rsandrini/D20-IRL-detection/3d_model/imgs/2.jpg

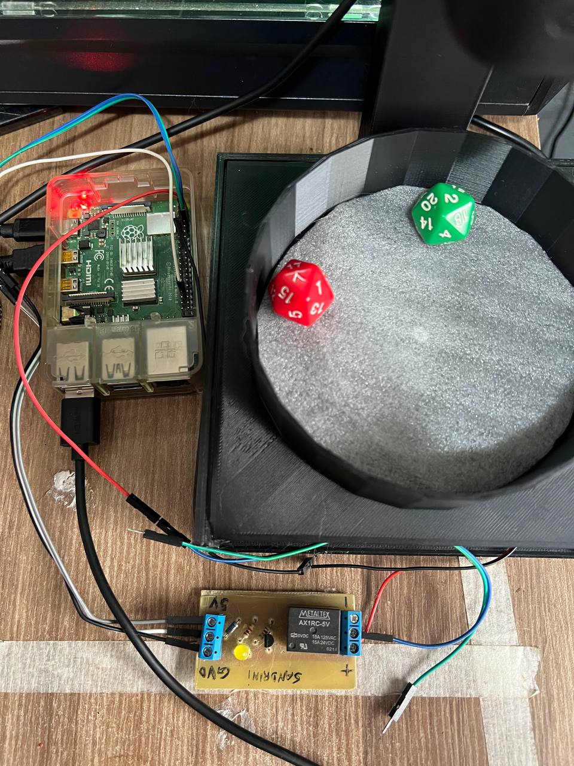
3d_model/imgs/2.jpg
