rsandrini/D20-IRL-detection/3d_model/imgs/3.jpg

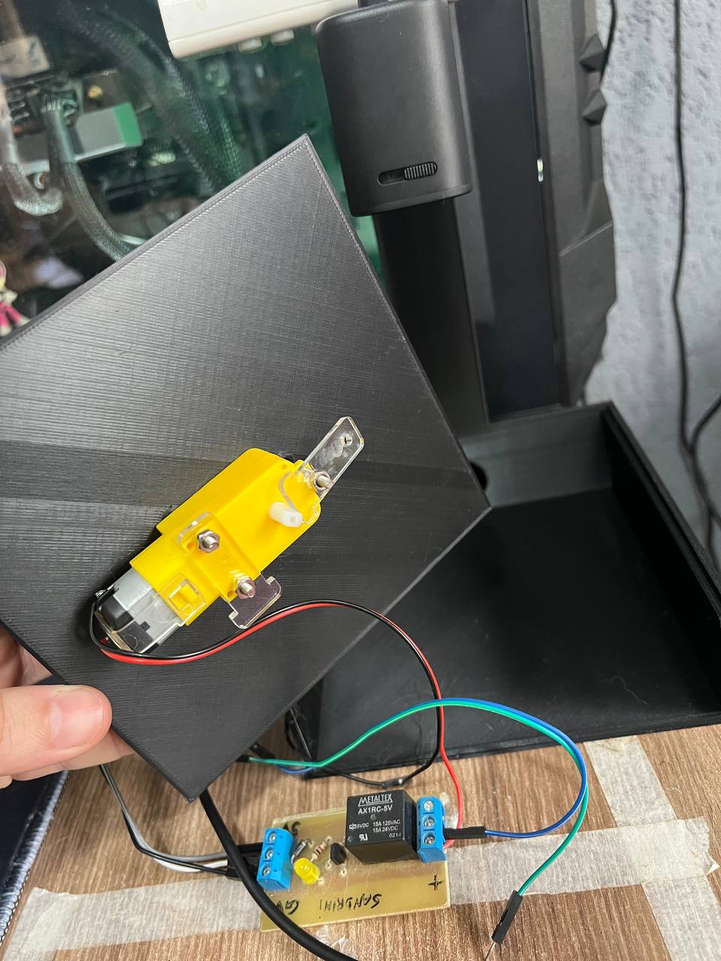
3d_model/imgs/3.jpg
