rsandrini/D20-IRL-detection/3d_model/imgs/4.jpg

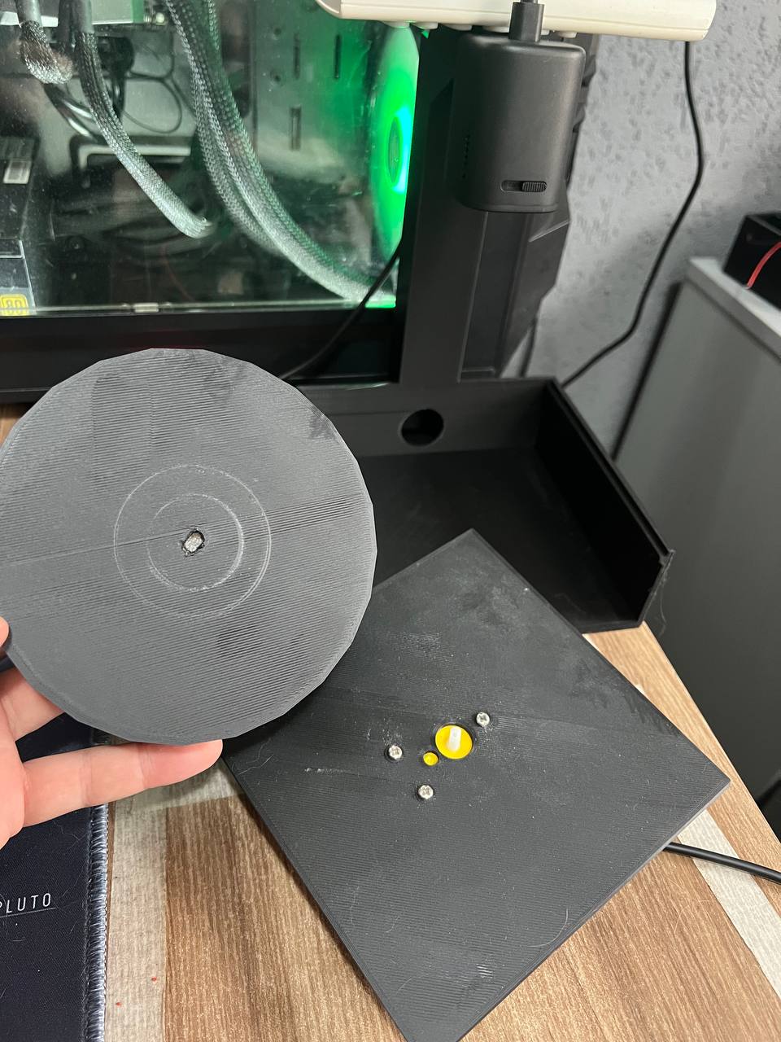
3d_model/imgs/4.jpg
