rsandrini/D20-IRL-detection/3d_model/imgs/5.jpg

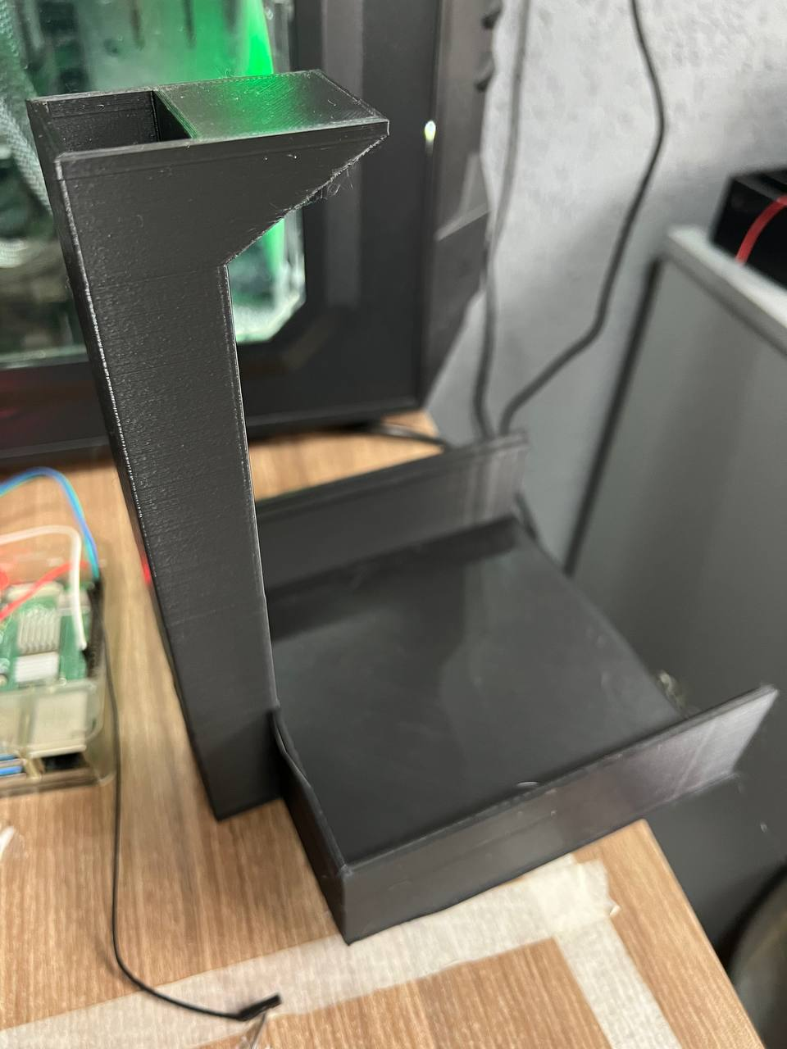
3d_model/imgs/5.jpg
