rsandrini/D20-IRL-detection/data/images/val/roll_0003_9260f4.jpg

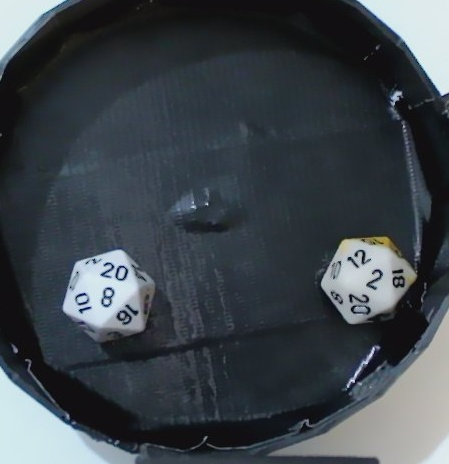
data/images/val/roll_0003_9260f4.jpg
