rsandrini/D20-IRL-detection/data/images/val/roll_0004_5c2b91.jpg

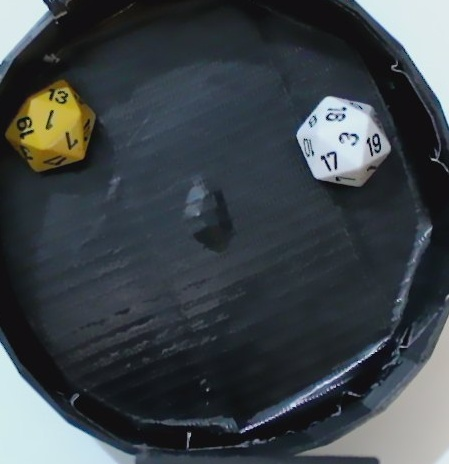
data/images/val/roll_0004_5c2b91.jpg
