rsandrini/D20-IRL-detection/data/images/val/roll_0006_699569.jpg

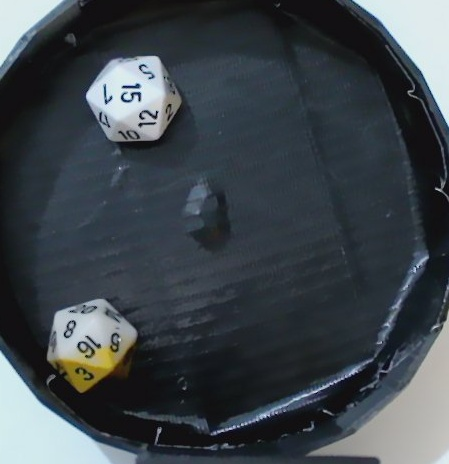
data/images/val/roll_0006_699569.jpg
