rsandrini/D20-IRL-detection/data/images/val/roll_0013_bd96cc.jpg

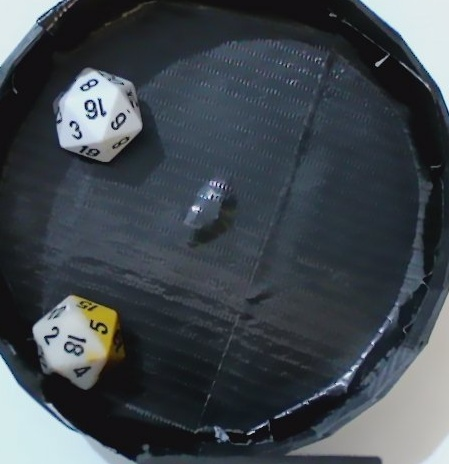
data/images/val/roll_0013_bd96cc.jpg
