rsandrini/D20-IRL-detection/data/images/val/roll_0014_3a582c.jpg

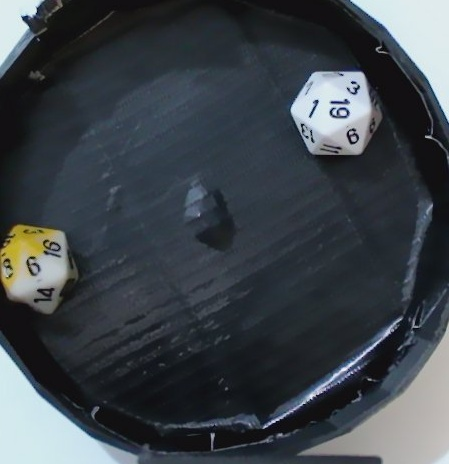
data/images/val/roll_0014_3a582c.jpg
