rsandrini/D20-IRL-detection/data/images/val/roll_0016_4558c0.jpg

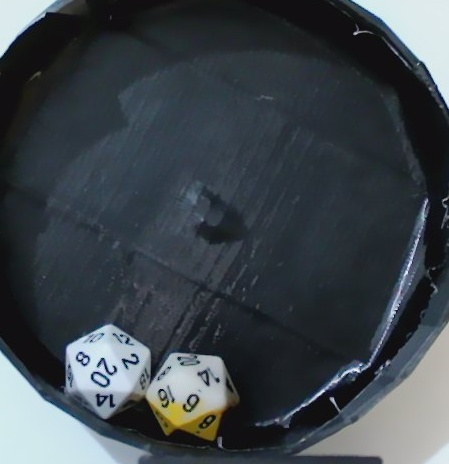
data/images/val/roll_0016_4558c0.jpg
