rsandrini/D20-IRL-detection/data/images/val/roll_0031_e9eac3.jpg

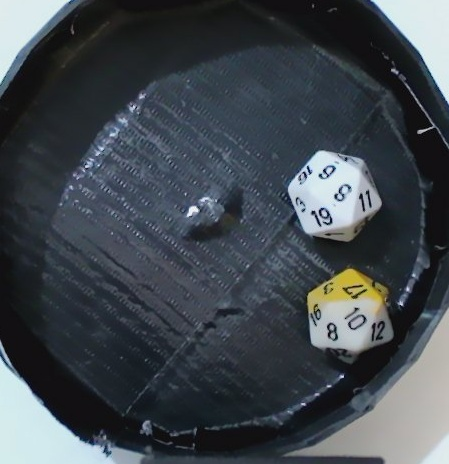
data/images/val/roll_0031_e9eac3.jpg
