rsandrini/D20-IRL-detection/data/images/val/roll_0033_6a69eb.jpg

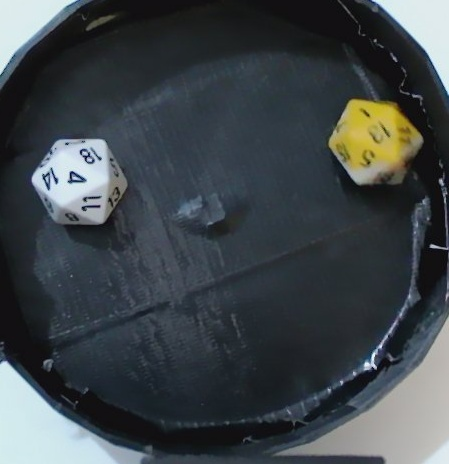
data/images/val/roll_0033_6a69eb.jpg
