rsandrini/D20-IRL-detection/data/images/val/roll_0037_a4c2fc.jpg

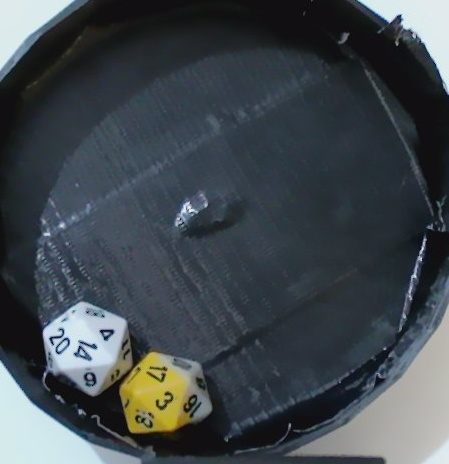
data/images/val/roll_0037_a4c2fc.jpg
