rsandrini/D20-IRL-detection/data/images/val/roll_0038_ef2dc1.jpg

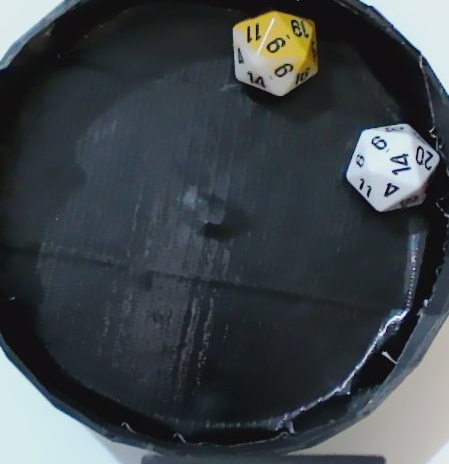
data/images/val/roll_0038_ef2dc1.jpg
