rsandrini/D20-IRL-detection/data/images/val/roll_0043_4cf03e.jpg

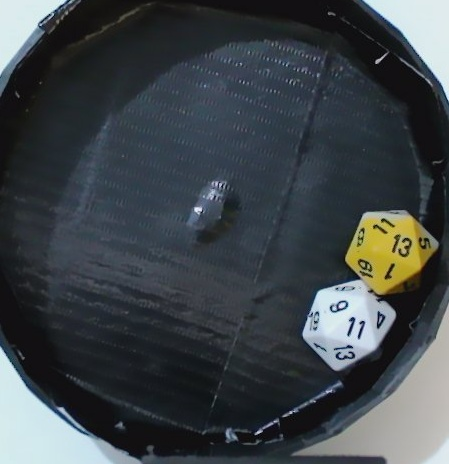
data/images/val/roll_0043_4cf03e.jpg
