rsandrini/D20-IRL-detection/data/images/val/roll_0045_0b2040.jpg

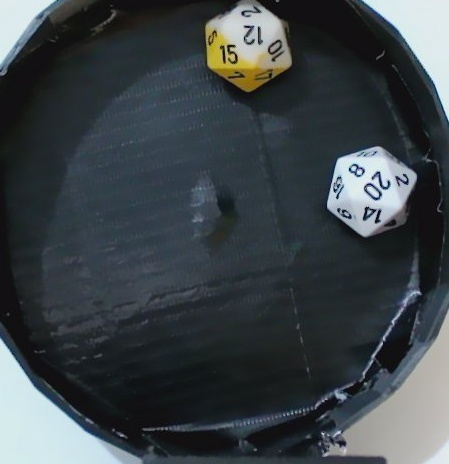
data/images/val/roll_0045_0b2040.jpg
