rsandrini/D20-IRL-detection/data/images/val/roll_0046_d0351c.jpg

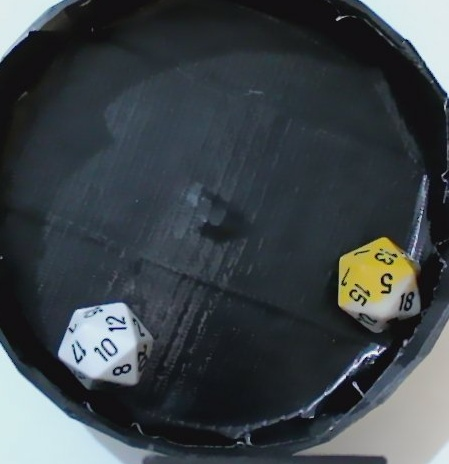
data/images/val/roll_0046_d0351c.jpg
