rsandrini/D20-IRL-detection/data/images/val/roll_0048_6ab94f.jpg

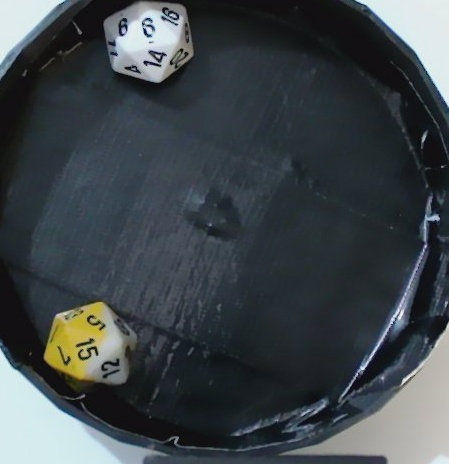
data/images/val/roll_0048_6ab94f.jpg
