rsandrini/D20-IRL-detection/data/images/val/roll_0062_7c9000.jpg

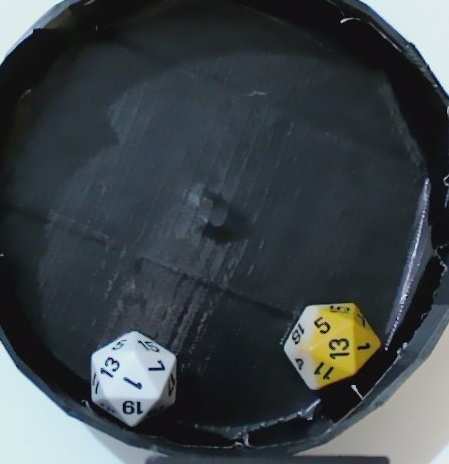
data/images/val/roll_0062_7c9000.jpg
