rsandrini/D20-IRL-detection/data/images/val/roll_0065_9c6021.jpg

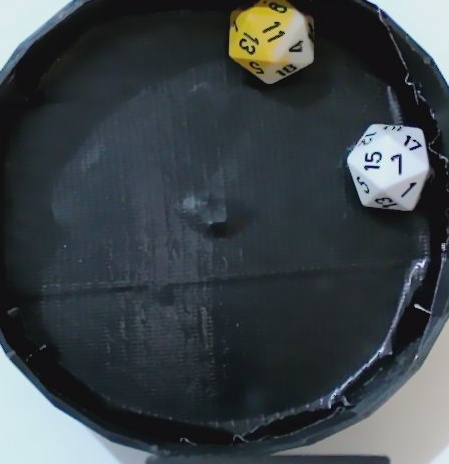
data/images/val/roll_0065_9c6021.jpg
