rsandrini/D20-IRL-detection/data/images/val/roll_0067_908758.jpg

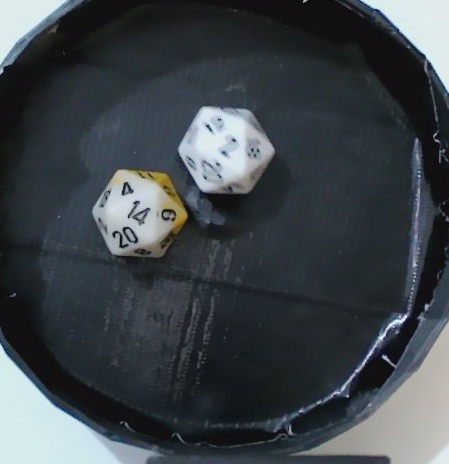
data/images/val/roll_0067_908758.jpg
