rsandrini/D20-IRL-detection/data/images/val/roll_0070_61421d.jpg

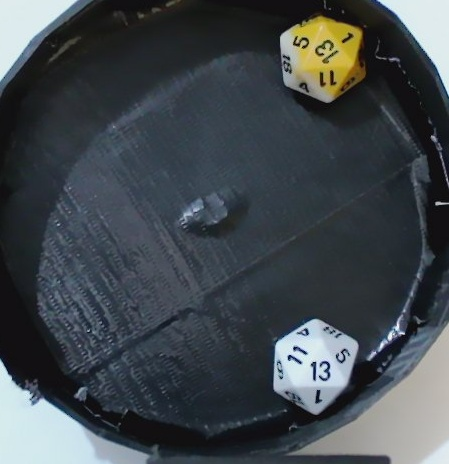
data/images/val/roll_0070_61421d.jpg
