rsandrini/D20-IRL-detection/data/images/val/roll_0077_c047f7.jpg

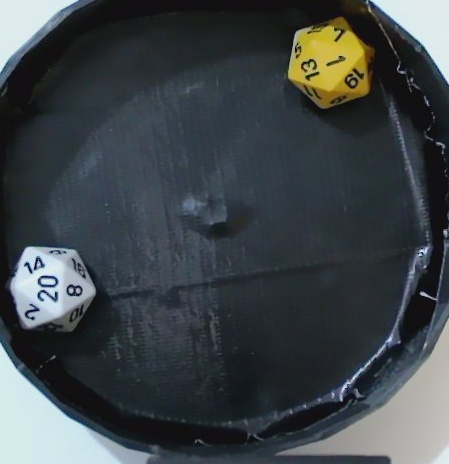
data/images/val/roll_0077_c047f7.jpg
