rsandrini/D20-IRL-detection/data/images/val/roll_0102_18575e.jpg

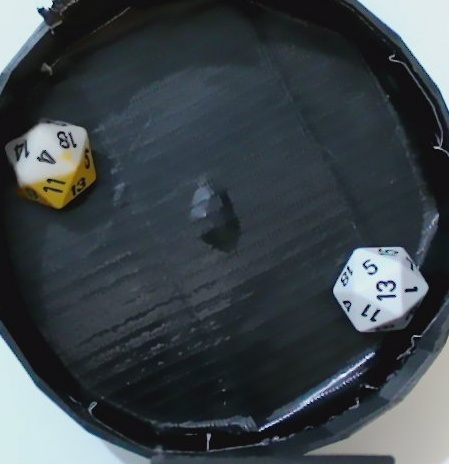
data/images/val/roll_0102_18575e.jpg
