rsandrini/D20-IRL-detection/data/images/val/roll_0111_e147ee.jpg

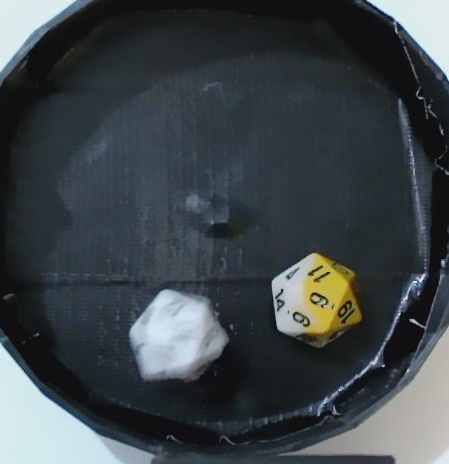
data/images/val/roll_0111_e147ee.jpg
