rsandrini/D20-IRL-detection/data/images/val/roll_0112_fa6df9.jpg

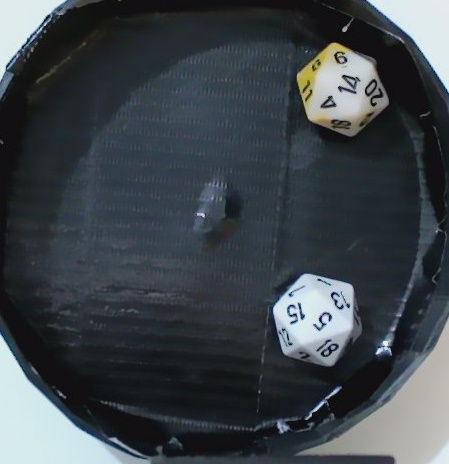
data/images/val/roll_0112_fa6df9.jpg
