rsandrini/D20-IRL-detection/data/images/val/roll_0122_8daa32.jpg

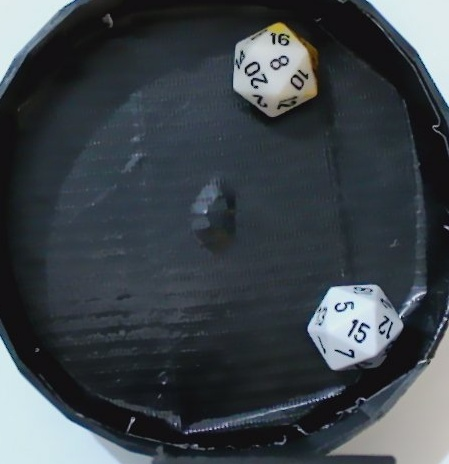
data/images/val/roll_0122_8daa32.jpg
