rsandrini/D20-IRL-detection/data/images/val/roll_0123_5c0753.jpg

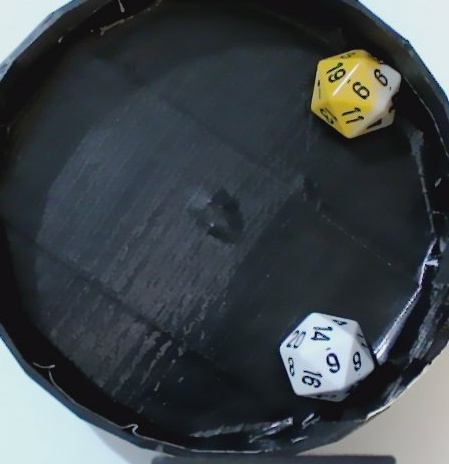
data/images/val/roll_0123_5c0753.jpg
