rsandrini/D20-IRL-detection/data/images/val/roll_0127_2e7928.jpg

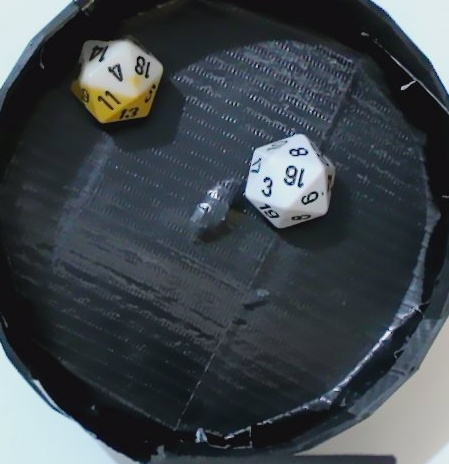
data/images/val/roll_0127_2e7928.jpg
