rsandrini/D20-IRL-detection/data/images/val/roll_0129_56e177.jpg

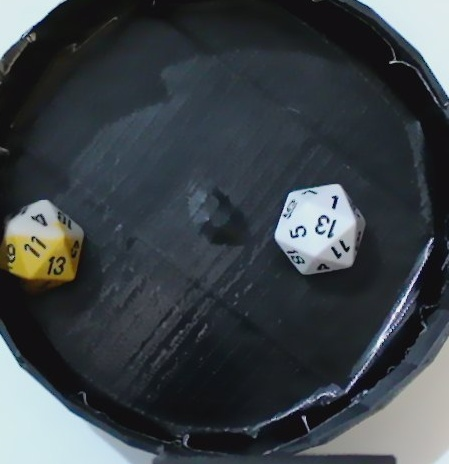
data/images/val/roll_0129_56e177.jpg
