rsandrini/D20-IRL-detection/data/images/val/roll_0131_5401d8.jpg

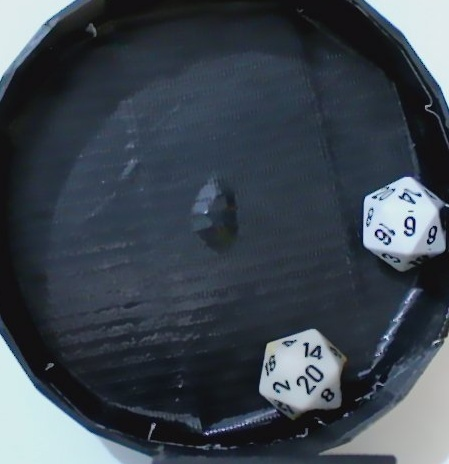
data/images/val/roll_0131_5401d8.jpg
