rsandrini/D20-IRL-detection/data/images/val/roll_0137_ff023d.jpg

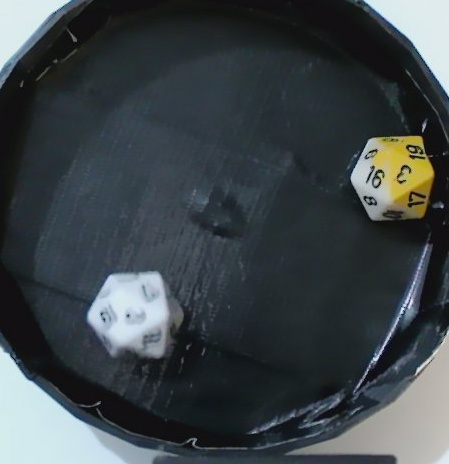
data/images/val/roll_0137_ff023d.jpg
