rsandrini/D20-IRL-detection/data/images/val/roll_0154_236faf.jpg

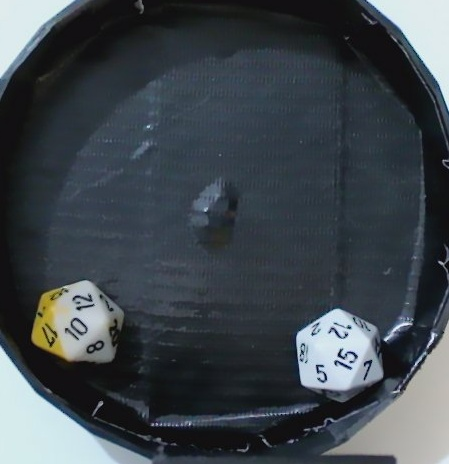
data/images/val/roll_0154_236faf.jpg
