rsandrini/D20-IRL-detection/data/images/val/roll_0159_bd059c.jpg

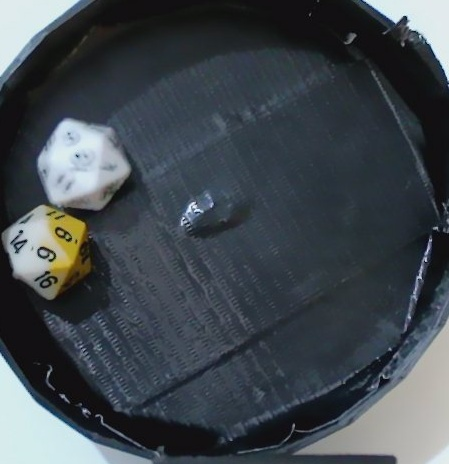
data/images/val/roll_0159_bd059c.jpg
