rsandrini/D20-IRL-detection/data/images/val/roll_0160_444020.jpg

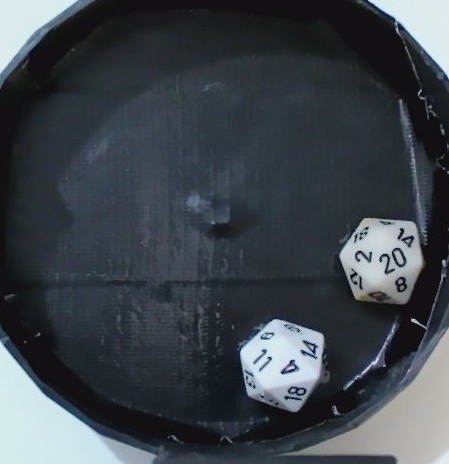
data/images/val/roll_0160_444020.jpg
