rsandrini/D20-IRL-detection/data/images/val/roll_0163_bad7c1.jpg

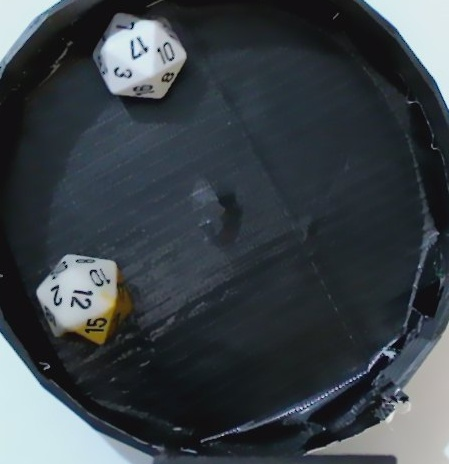
data/images/val/roll_0163_bad7c1.jpg
