rsandrini/D20-IRL-detection/data/images/val/roll_0168_1e1c85.jpg

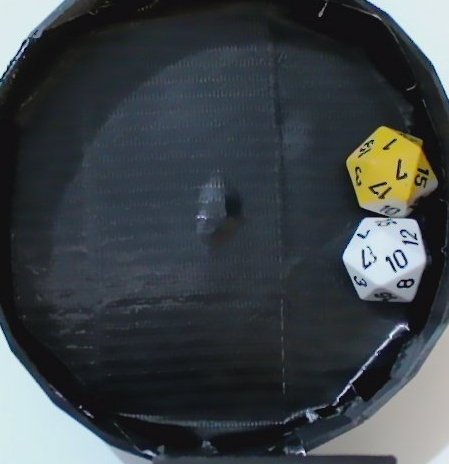
data/images/val/roll_0168_1e1c85.jpg
