rsandrini/D20-IRL-detection/data/images/val/roll_0171_e6abc9.jpg

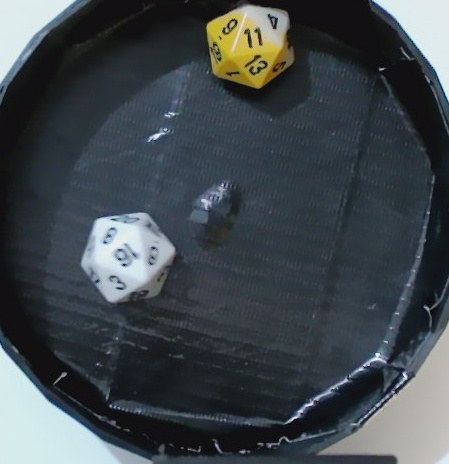
data/images/val/roll_0171_e6abc9.jpg
