rsandrini/D20-IRL-detection/data/images/val/roll_0173_381584.jpg

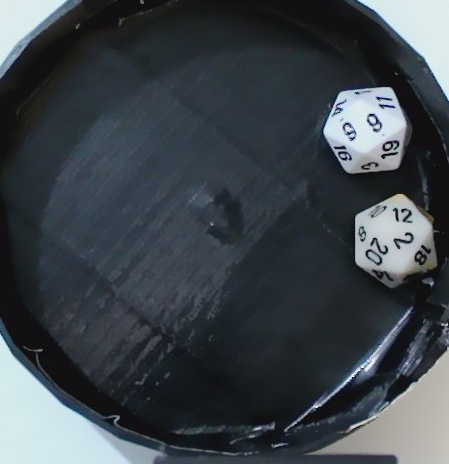
data/images/val/roll_0173_381584.jpg
