rsandrini/D20-IRL-detection/data/images/val/roll_0187_8b234c.jpg

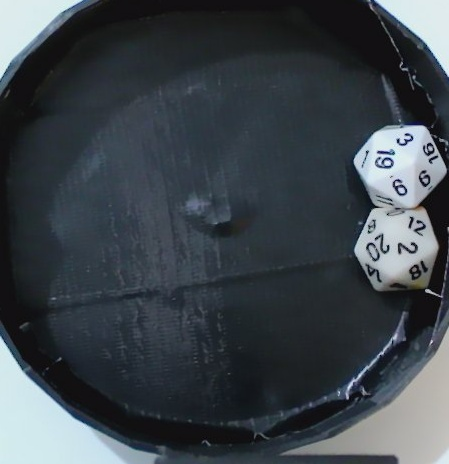
data/images/val/roll_0187_8b234c.jpg
