rsandrini/D20-IRL-detection/data/images/val/roll_0188_95a398.jpg

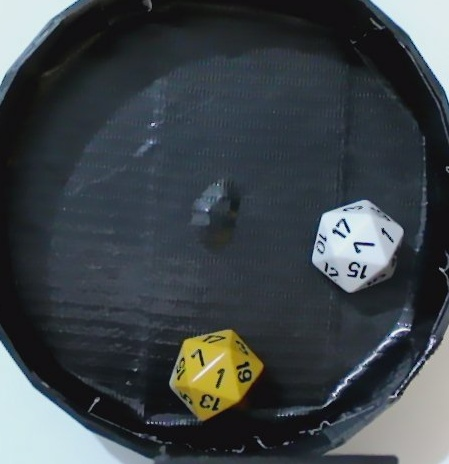
data/images/val/roll_0188_95a398.jpg
