rsandrini/D20-IRL-detection/data/images/val/roll_0194_2706d9.jpg

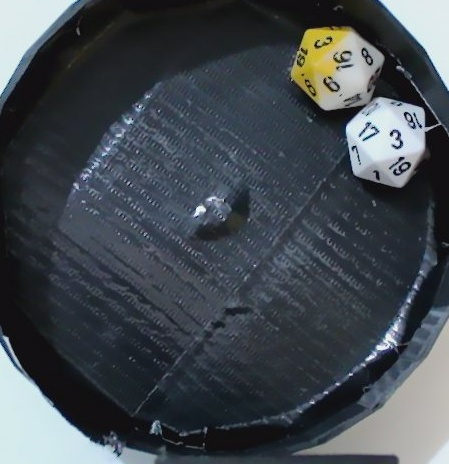
data/images/val/roll_0194_2706d9.jpg
