rsandrini/D20-IRL-detection/data/images/val/roll_0195_a73f36.jpg

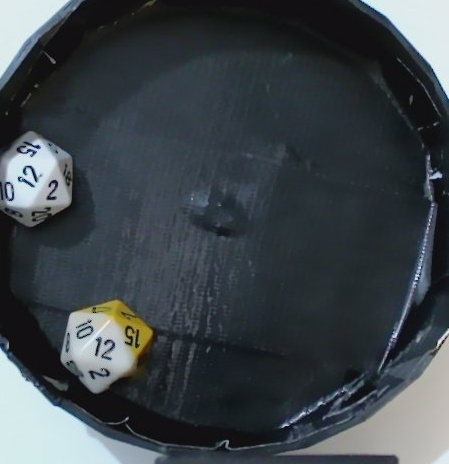
data/images/val/roll_0195_a73f36.jpg
