rsandrini/D20-IRL-detection/data/images/val/roll_0196_e32400.jpg

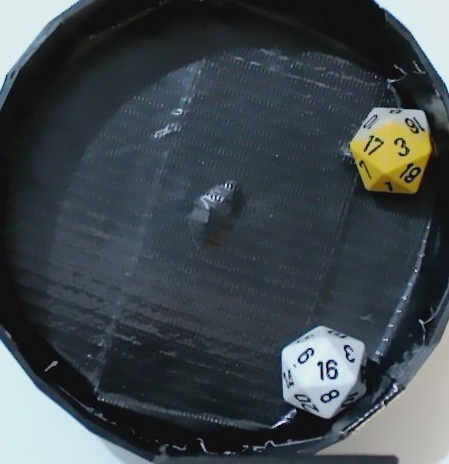
data/images/val/roll_0196_e32400.jpg
