rsandrini/D20-IRL-detection/static/results/0ec7581d-a79f-41ec-bebb-41047d4bcfe1.jpg

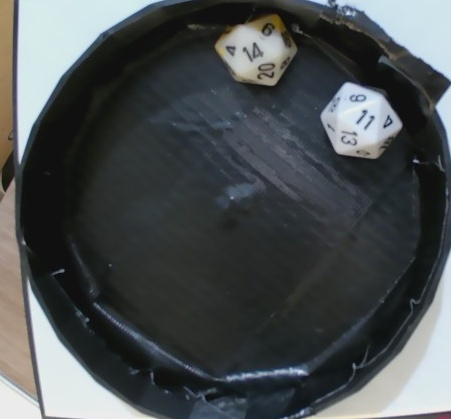
static/results/0ec7581d-a79f-41ec-bebb-41047d4bcfe1.jpg
