rsandrini/D20-IRL-detection/static/results/1f2905ae-a408-4a8b-bb5f-29edec2092f3.jpg

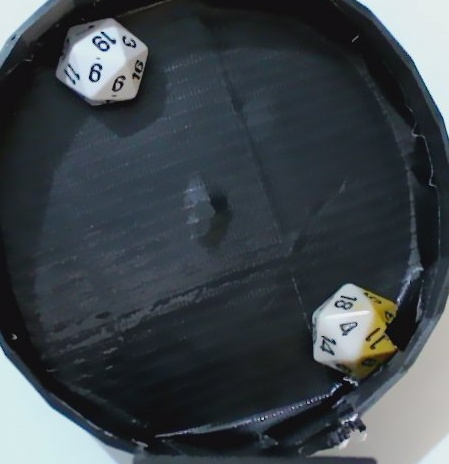
static/results/1f2905ae-a408-4a8b-bb5f-29edec2092f3.jpg
