rsandrini/D20-IRL-detection/static/results/2d5dee4a-9d91-4876-b8cb-90a706628ac4.jpg

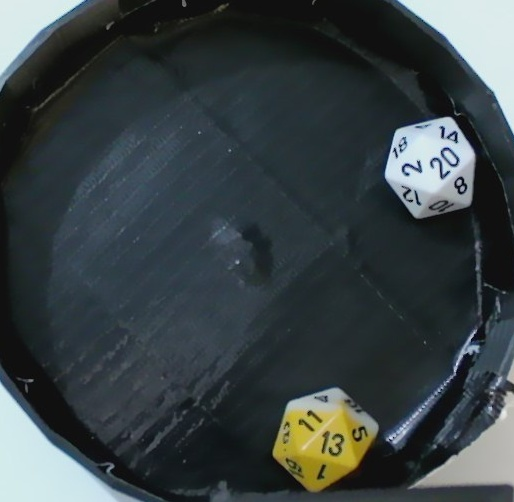
static/results/2d5dee4a-9d91-4876-b8cb-90a706628ac4.jpg
