rsandrini/D20-IRL-detection/static/results/63ee4cc3-fca6-4ec0-a35e-1c4646e539cd.gif

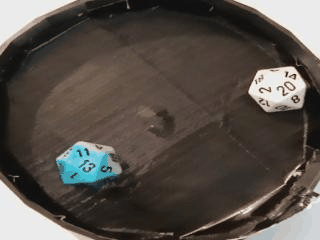
static/results/63ee4cc3-fca6-4ec0-a35e-1c4646e539cd.gif
