rsandrini/D20-IRL-detection/static/results/75d9a677-4451-443c-803d-1ba4c33d57f9.jpg

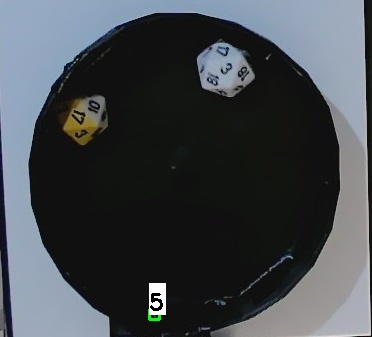
static/results/75d9a677-4451-443c-803d-1ba4c33d57f9.jpg
