rsandrini/D20-IRL-detection/static/results/223f2116-806a-4e07-b7c2-eb1def2b251b.jpg

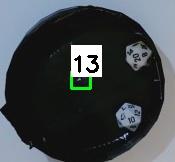
static/results/223f2116-806a-4e07-b7c2-eb1def2b251b.jpg
