rsandrini/D20-IRL-detection/static/results/428e884d-69d0-4718-a8a9-e1feac12c718.jpg

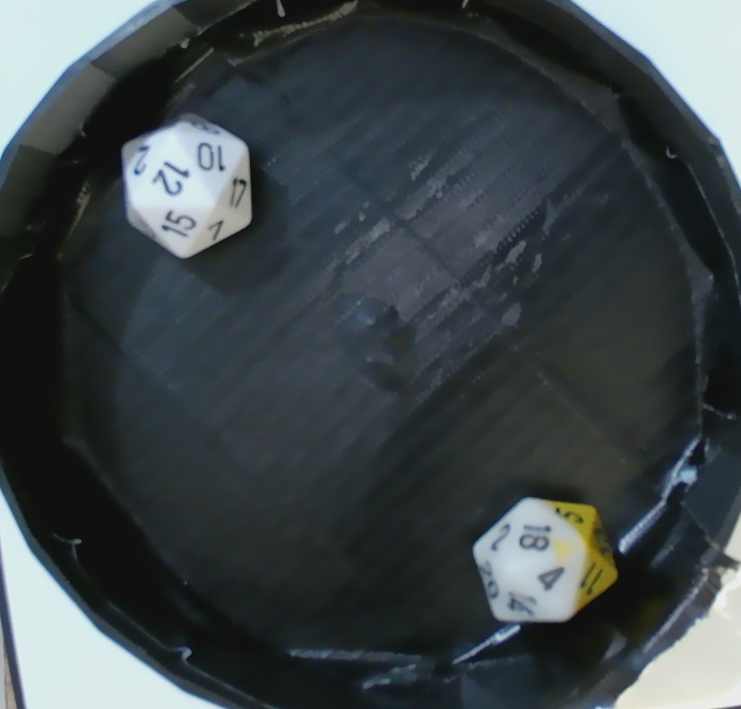
static/results/428e884d-69d0-4718-a8a9-e1feac12c718.jpg
