rsandrini/D20-IRL-detection/static/results/505b5c6e-b854-461b-a9c2-39d6cff4a146.jpg

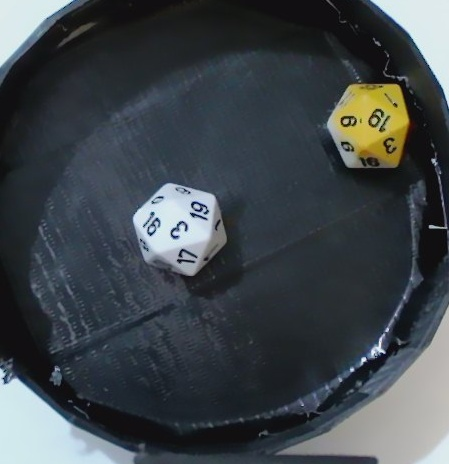
static/results/505b5c6e-b854-461b-a9c2-39d6cff4a146.jpg
