rsandrini/D20-IRL-detection/static/results/600d41de-3759-4a8f-982c-8f376b47929a.jpg

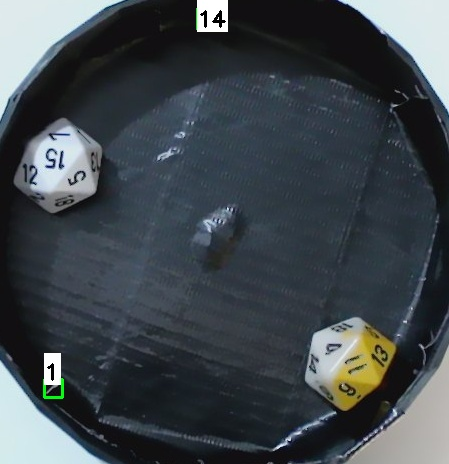
static/results/600d41de-3759-4a8f-982c-8f376b47929a.jpg
