rsandrini/D20-IRL-detection/static/results/2539a522-f37b-4129-82e0-7a8c40de38be.jpg

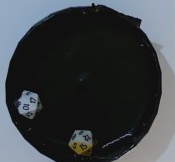
static/results/2539a522-f37b-4129-82e0-7a8c40de38be.jpg
