rsandrini/D20-IRL-detection/static/results/2985c857-9b9b-49bc-b022-46b17c431721.gif

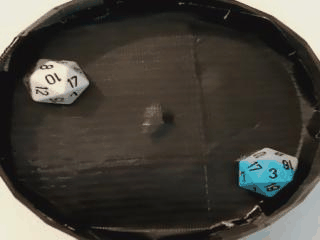
static/results/2985c857-9b9b-49bc-b022-46b17c431721.gif
