rsandrini/D20-IRL-detection/static/results/4426a67b-6e3e-4b60-9d31-17f29a3e8788.jpg

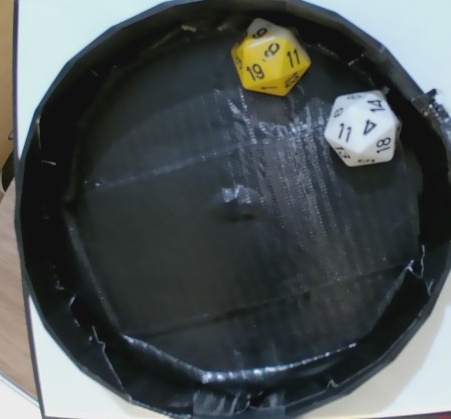
static/results/4426a67b-6e3e-4b60-9d31-17f29a3e8788.jpg
