rsandrini/D20-IRL-detection/static/results/42641748-526f-4314-aae3-439b0b9f9e85.jpg

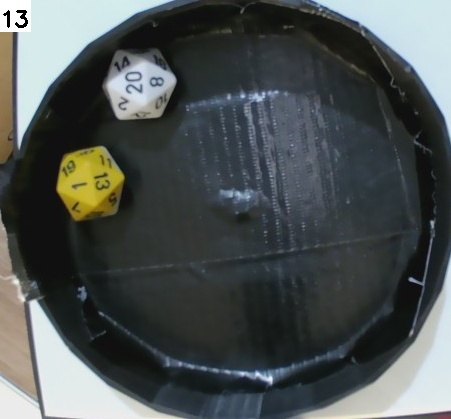
static/results/42641748-526f-4314-aae3-439b0b9f9e85.jpg
