rsandrini/D20-IRL-detection/static/results/df58865e-708a-4e75-8b74-b39ae49331ff.jpg

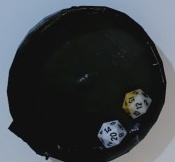
static/results/df58865e-708a-4e75-8b74-b39ae49331ff.jpg
