rsandrini/D20-IRL-detection/static/results/eb8a9b36-dcb0-4fa9-ad2c-afa261924b8b.jpg

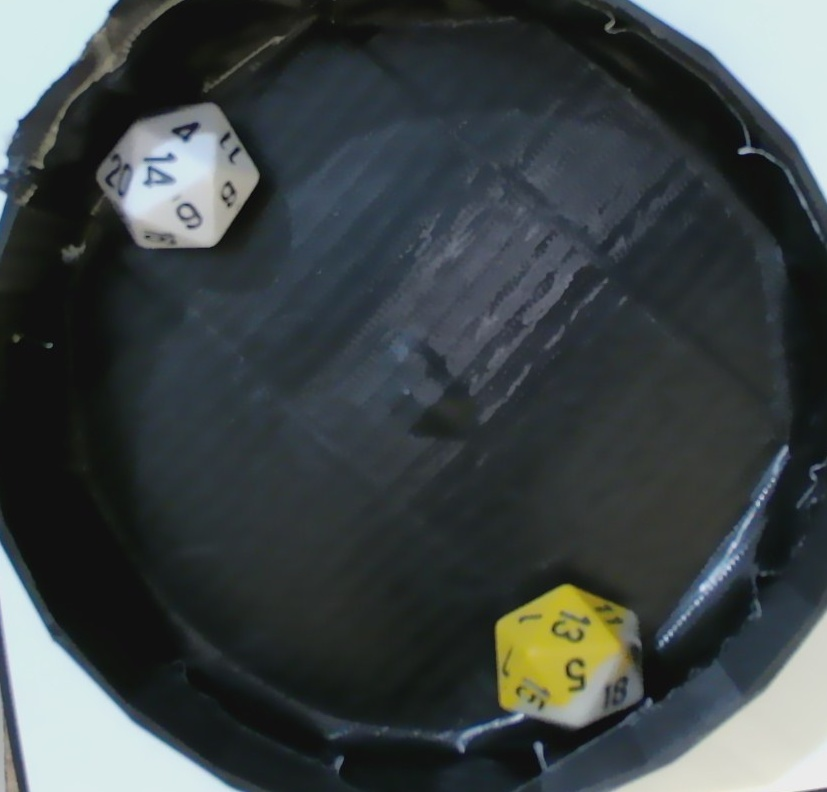
static/results/eb8a9b36-dcb0-4fa9-ad2c-afa261924b8b.jpg
