rsandrini/D20-IRL-detection/static/results/f77a6ad1-427b-4974-91a9-76c40a6d492a.jpg

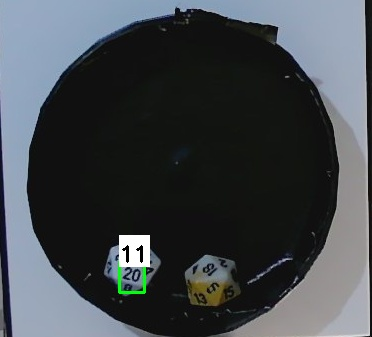
static/results/f77a6ad1-427b-4974-91a9-76c40a6d492a.jpg
