rsandrini/D20-IRL-detection/object_detection.py

import os
import cv2
import numpy as np
try:
    from ai_edge_litert.interpreter import Interpreter
except ImportError:
    from tflite_runtime.interpreter import Interpreter


class ObjectDetector:
    def __init__(self, model_dir):
        self.model_dir = model_dir
        self.min_conf_threshold = 0.3
        self.nms_threshold = 0.45
        self.labels = [str(i) for i in range(1, 21)]
        self.interpreter = None
        model_path = os.path.join(self.model_dir, "detect.tflite")
        if not os.path.exists(model_path):
            print(f"WARNING: No model found at '{model_path}'. Detection disabled until model is deployed.")
            return
        self.load_model()

    def load_model(self):
        model_path = os.path.join(self.model_dir, "detect.tflite")
        self.interpreter = Interpreter(model_path=model_path)
        self.interpreter.allocate_tensors()
        self.input_details = self.interpreter.get_input_details()
        self.output_details = self.interpreter.get_output_details()
        self.input_height = self.input_details[0]["shape"][1]
        self.input_width = self.input_details[0]["shape"][2]
        self.is_quantized = self.input_details[0]["dtype"] == np.uint8

    def _preprocess(self, image):
        image_rgb = cv2.cvtColor(image, cv2.COLOR_BGR2RGB)
        resized = cv2.resize(image_rgb, (self.input_width, self.input_height))
        input_data = np.expand_dims(resized, axis=0)
        if self.is_quantized:
            return input_data.astype(np.uint8)
        return (input_data.astype(np.float32) / 255.0)

    def detect_array(self, image: np.ndarray) -> list:
        """Run inference on a BGR numpy array. Returns same format as detect_objects."""
        if self.interpreter is None:
            return []
        imH, imW = image.shape[:2]

        self.interpreter.set_tensor(self.input_details[0]["index"], self._preprocess(image))
        self.interpreter.invoke()

        output = np.squeeze(self.interpreter.get_tensor(self.output_details[0]["index"])).T
        boxes_raw = output[:, :4]
        class_scores = output[:, 4:]

        class_ids = np.argmax(class_scores, axis=1)
        confidences = class_scores[np.arange(len(class_scores)), class_ids]

        mask = confidences >= self.min_conf_threshold
        if not mask.any():
            return []

        boxes_raw = boxes_raw[mask]
        confidences = confidences[mask]
        class_ids = class_ids[mask]

        xmin = np.clip((boxes_raw[:, 0] - boxes_raw[:, 2] / 2) * imW, 0, imW).astype(int)
        ymin = np.clip((boxes_raw[:, 1] - boxes_raw[:, 3] / 2) * imH, 0, imH).astype(int)
        bw = (boxes_raw[:, 2] * imW).astype(int)
        bh = (boxes_raw[:, 3] * imH).astype(int)

        nms_boxes = [[int(x), int(y), int(w), int(h)] for x, y, w, h in zip(xmin, ymin, bw, bh)]
        indices = cv2.dnn.NMSBoxes(nms_boxes, confidences.tolist(), self.min_conf_threshold, self.nms_threshold)
        if len(indices) == 0:
            return []

        detections = []
        for i in indices.flatten()[:2]:
            label = self.labels[class_ids[i]]
            x, y, w, h = nms_boxes[i]
            detections.append({
                "face": int(label),
                "confidence": round(float(confidences[i]), 4),
                "bbox": [int(x), int(y), int(x + w), int(y + h)],
            })
        return detections

    def detect_objects(self, image_path, image_name):
        """Run inference and return list of dicts: {face, confidence, bbox [x1,y1,x2,y2]}."""
        if self.interpreter is None:
            return []
        image_path_file = os.path.join(image_path, image_name)
        image = cv2.imread(image_path_file)
        imH, imW = image.shape[:2]

        self.interpreter.set_tensor(self.input_details[0]["index"], self._preprocess(image))
        self.interpreter.invoke()

        # YOLOv8 TFLite output: [1, 4+nc, num_anchors] — transpose to [num_anchors, 4+nc]
        output = np.squeeze(self.interpreter.get_tensor(self.output_details[0]["index"])).T
        boxes_raw = output[:, :4]      # cx, cy, w, h in input image pixel coords
        class_scores = output[:, 4:]   # nc scores per anchor

        class_ids = np.argmax(class_scores, axis=1)
        confidences = class_scores[np.arange(len(class_scores)), class_ids]

        mask = confidences >= self.min_conf_threshold
        if not mask.any():
            return []

        boxes_raw = boxes_raw[mask]
        confidences = confidences[mask]
        class_ids = class_ids[mask]

        # Boxes are normalized (0-1) — scale directly to original image size
        xmin = np.clip((boxes_raw[:, 0] - boxes_raw[:, 2] / 2) * imW, 0, imW).astype(int)
        ymin = np.clip((boxes_raw[:, 1] - boxes_raw[:, 3] / 2) * imH, 0, imH).astype(int)
        bw = (boxes_raw[:, 2] * imW).astype(int)
        bh = (boxes_raw[:, 3] * imH).astype(int)

        nms_boxes = [[int(x), int(y), int(w), int(h)] for x, y, w, h in zip(xmin, ymin, bw, bh)]
        indices = cv2.dnn.NMSBoxes(nms_boxes, confidences.tolist(), self.min_conf_threshold, self.nms_threshold)
        if len(indices) == 0:
            return []

        detections = []
        for i in indices.flatten()[:2]:
            label = self.labels[class_ids[i]]
            x, y, w, h = nms_boxes[i]
            x2, y2 = x + w, y + h

            detections.append({
                "face": int(label),
                "confidence": round(float(confidences[i]), 4),
                "bbox": [int(x), int(y), int(x2), int(y2)],
            })

            cv2.rectangle(image, (x, y), (x2, y2), (10, 255, 0), 2)
            label_size, _ = cv2.getTextSize(label, cv2.FONT_HERSHEY_SIMPLEX, 0.7, 2)
            ly = max(y, label_size[1] + 10)
            cv2.rectangle(image, (x, ly - label_size[1] - 10), (x + label_size[0], ly + 5), (255, 255, 255), cv2.FILLED)
            cv2.putText(image, label, (x, ly), cv2.FONT_HERSHEY_SIMPLEX, 0.7, (0, 0, 0), 2)

        cv2.imwrite(image_path_file, image)
        return detections

    def crop_image(self, image_path, bbox, margin=20):
        """Crop image to bbox with margin, save as <stem>_crop.jpg, return new path."""
        image = cv2.imread(image_path)
        if image is None:
            return None
        imH, imW = image.shape[:2]
        x1, y1, x2, y2 = bbox
        x1 = max(0, x1 - margin)
        y1 = max(0, y1 - margin)
        x2 = min(imW, x2 + margin)
        y2 = min(imH, y2 + margin)
        cropped = image[y1:y2, x1:x2]
        stem, ext = os.path.splitext(image_path)
        crop_path = f"{stem}_crop{ext}"
        cv2.imwrite(crop_path, cropped)
        return crop_path
